alexanderjgshort/Leonhart/Multi_Protocol_Radio.kicad_sch

## KiCad design Multi_Protocol_Radio.kicad_sch (2026-04-30)

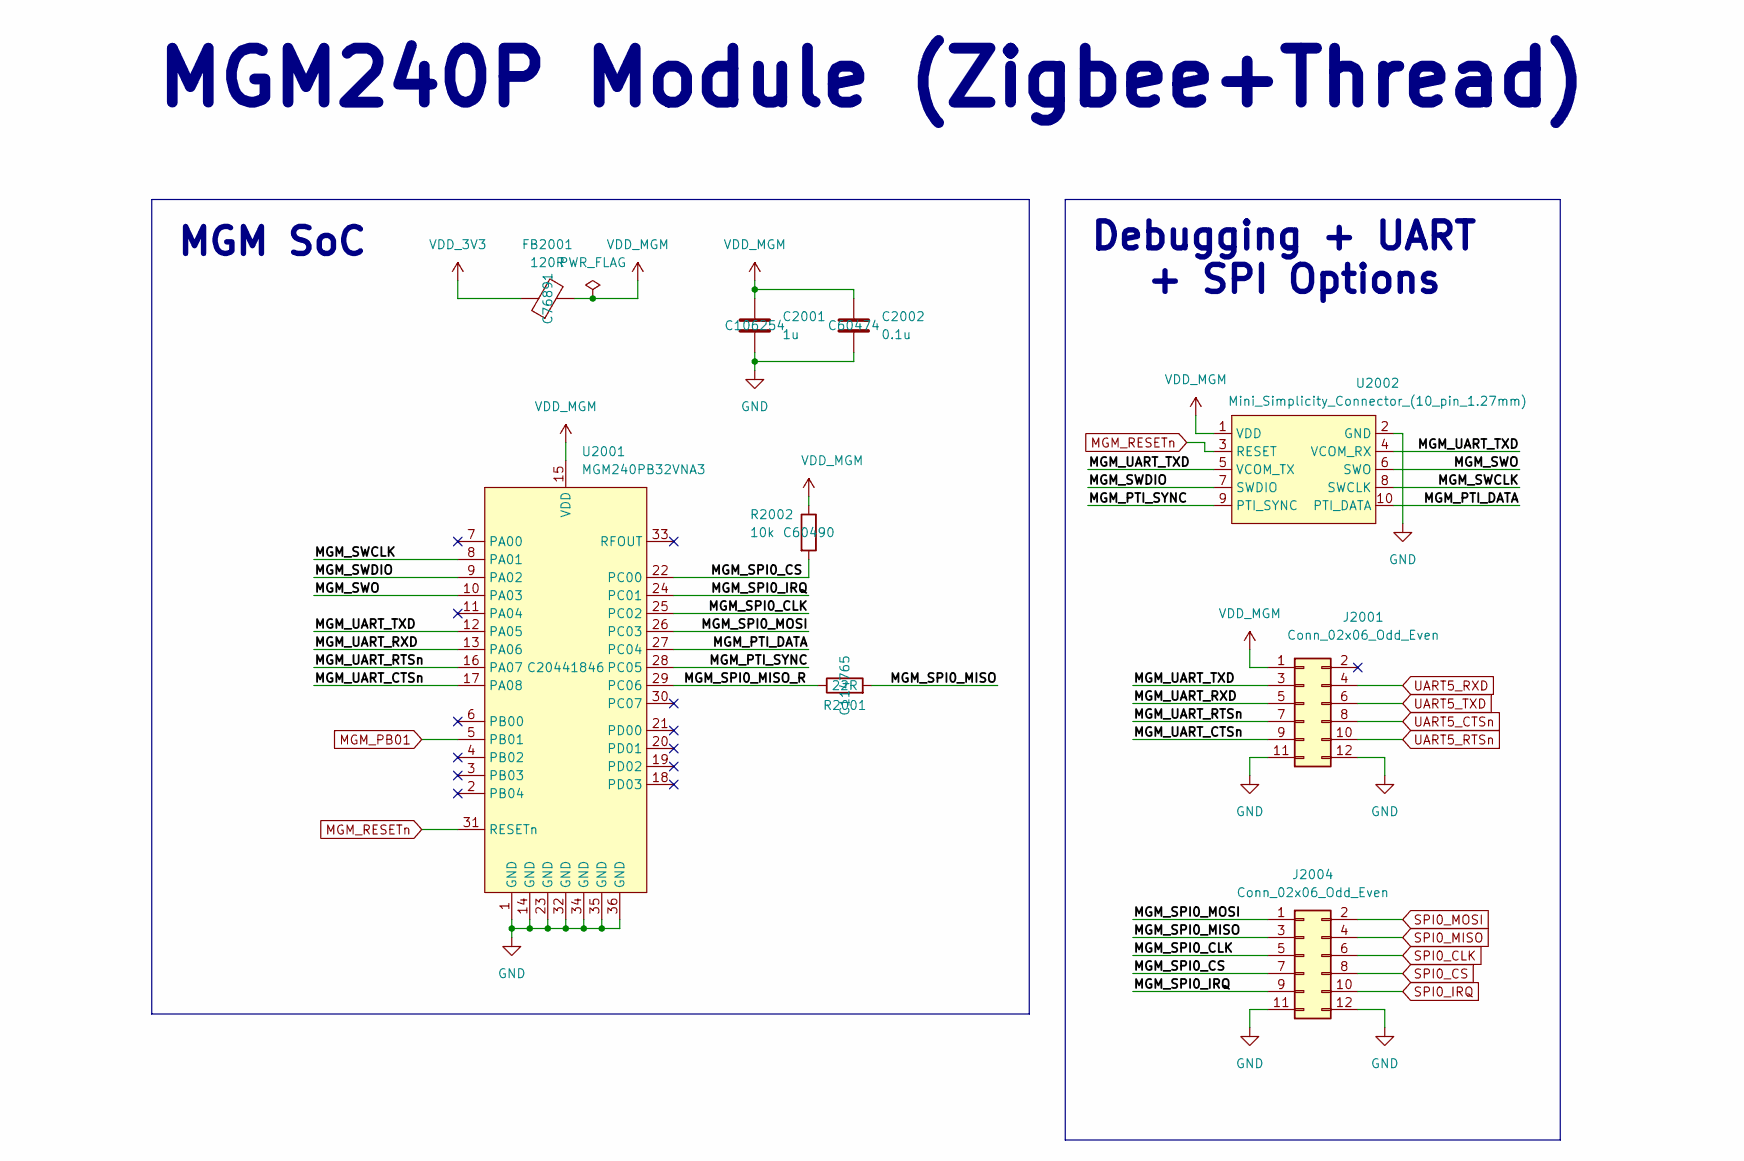
[picture p2: schematic Multi_Protocol_Radio.kicad_sch]

Parts:
C2001: 1u; C_0402_1005Metric; JLCPCB Part# C106254
C2002: 0.1u; C_0402_1005Metric; JLCPCB Part# C60474
FB2001: 120R; R_0402_1005Metric; JLCPCB Part# C76891
J2001, J2004: Conn_02x06_Odd_Even; PinHeader_2x06_P2.54mm_Vertical
R2001: 22R; R_0402_1005Metric; JLCPCB Part# C114765
R2002: 10k; R_0402_1005Metric; JLCPCB Part# C60490
U2001: MGM240PB32VNA3; JLCPCB Part# C20441846
U2002: Mini_Simplicity_Connector_(10_pin_1.27mm); FTSH10501LDVK

Connections:
GND: C2001.2, C2002.2, J2001.11, J2001.12, J2004.11, J2004.12, U2001.1 (GND), U2001.14 (GND), U2001.23 (GND), U2001.32 (GND), U2001.34 (GND), U2001.35 (GND), U2001.36 (GND), U2002.2 (GND)
MGM_PB01: U2001.5 (PB01)
MGM_PTI_DATA: U2001.27 (PC04), U2002.10 (PTI_DATA)
MGM_PTI_SYNC: U2001.28 (PC05), U2002.9 (PTI_SYNC)
MGM_RESETn: U2001.31 (RESETn), U2002.3 (RESET)
MGM_SPI0_CLK: J2004.5, U2001.25 (PC02)
MGM_SPI0_CS: J2004.7, R2002.2, U2001.22 (PC00)
MGM_SPI0_IRQ: J2004.9, U2001.24 (PC01)
MGM_SPI0_MISO: J2004.3, R2001.2
MGM_SPI0_MISO_R: R2001.1, U2001.29 (PC06)
MGM_SPI0_MOSI: J2004.1, U2001.26 (PC03)
MGM_SWCLK: U2001.8 (PA01), U2002.8 (SWCLK)
MGM_SWDIO: U2001.9 (PA02), U2002.7 (SWDIO)
MGM_SWO: U2001.10 (PA03), U2002.6 (SWO)
MGM_UART_CTSn: J2001.9, U2001.17 (PA08)
MGM_UART_RTSn: J2001.7, U2001.16 (PA07)
MGM_UART_RXD: J2001.5, U2001.13 (PA06)
MGM_UART_TXD: J2001.3, U2001.12 (PA05), U2002.4 (VCOM_RX), U2002.5 (VCOM_TX)
SPI0_CLK: J2004.6
SPI0_CS: J2004.8
SPI0_IRQ: J2004.10
SPI0_MISO: J2004.4
SPI0_MOSI: J2004.2
UART5_CTSn: J2001.8
UART5_RTSn: J2001.10
UART5_RXD: J2001.4
UART5_TXD: J2001.6
VDD_3V3: FB2001.1
VDD_MGM: C2001.1, C2002.1, FB2001.2, J2001.1, R2002.1, U2001.15 (VDD), U2002.1 (VDD)

Notes on the sheet:
Debugging + UART + SPI Options
MGM SoC
MGM240P Module (Zigbee+Thread)
