alexanderjgshort/Leonhart/hostsystem.kicad_sch

## KiCad design hostsystem.kicad_sch (2026-04-30)

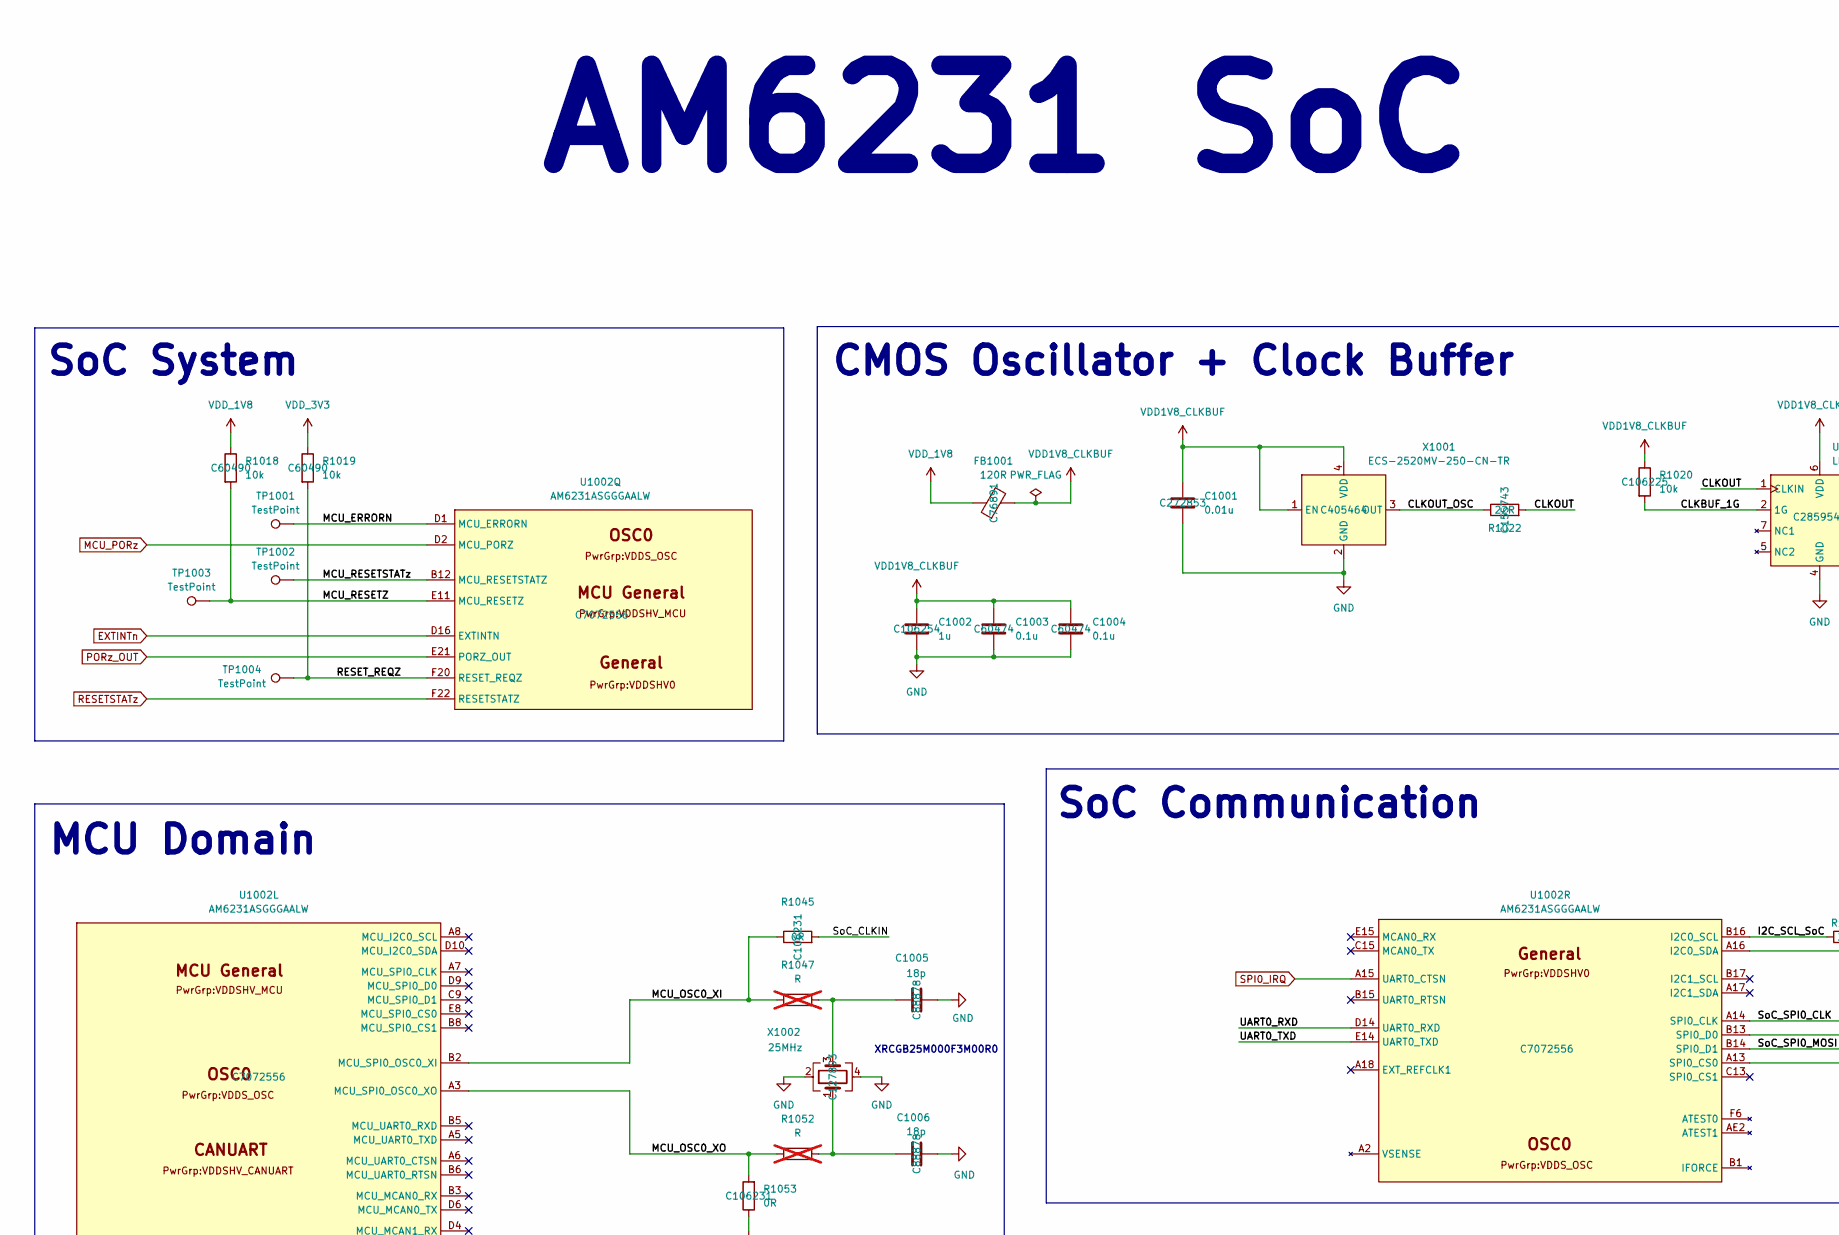
[picture p3: schematic hostsystem.kicad_sch, part in row 1, column 1]

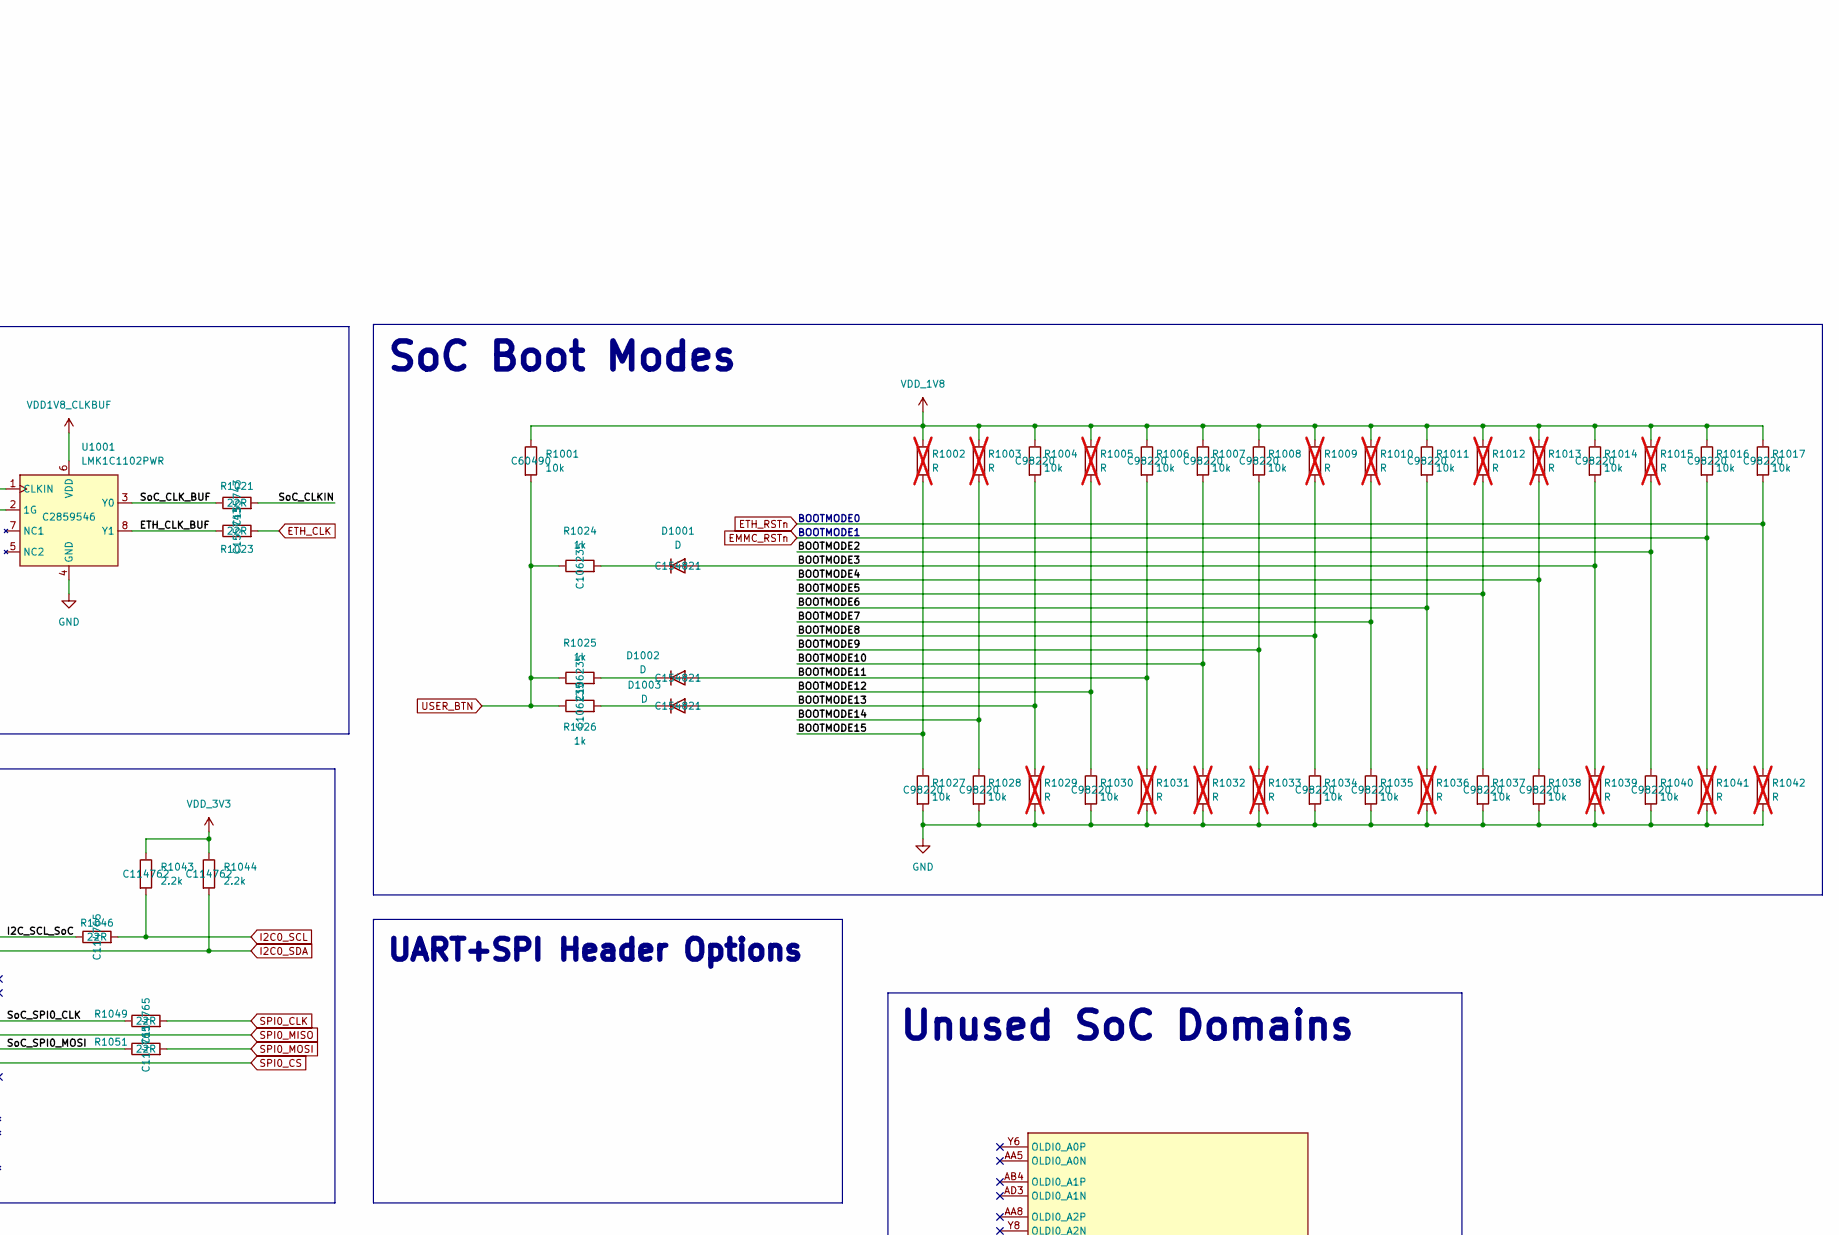
[picture p4: schematic hostsystem.kicad_sch, part in row 1, column 2]

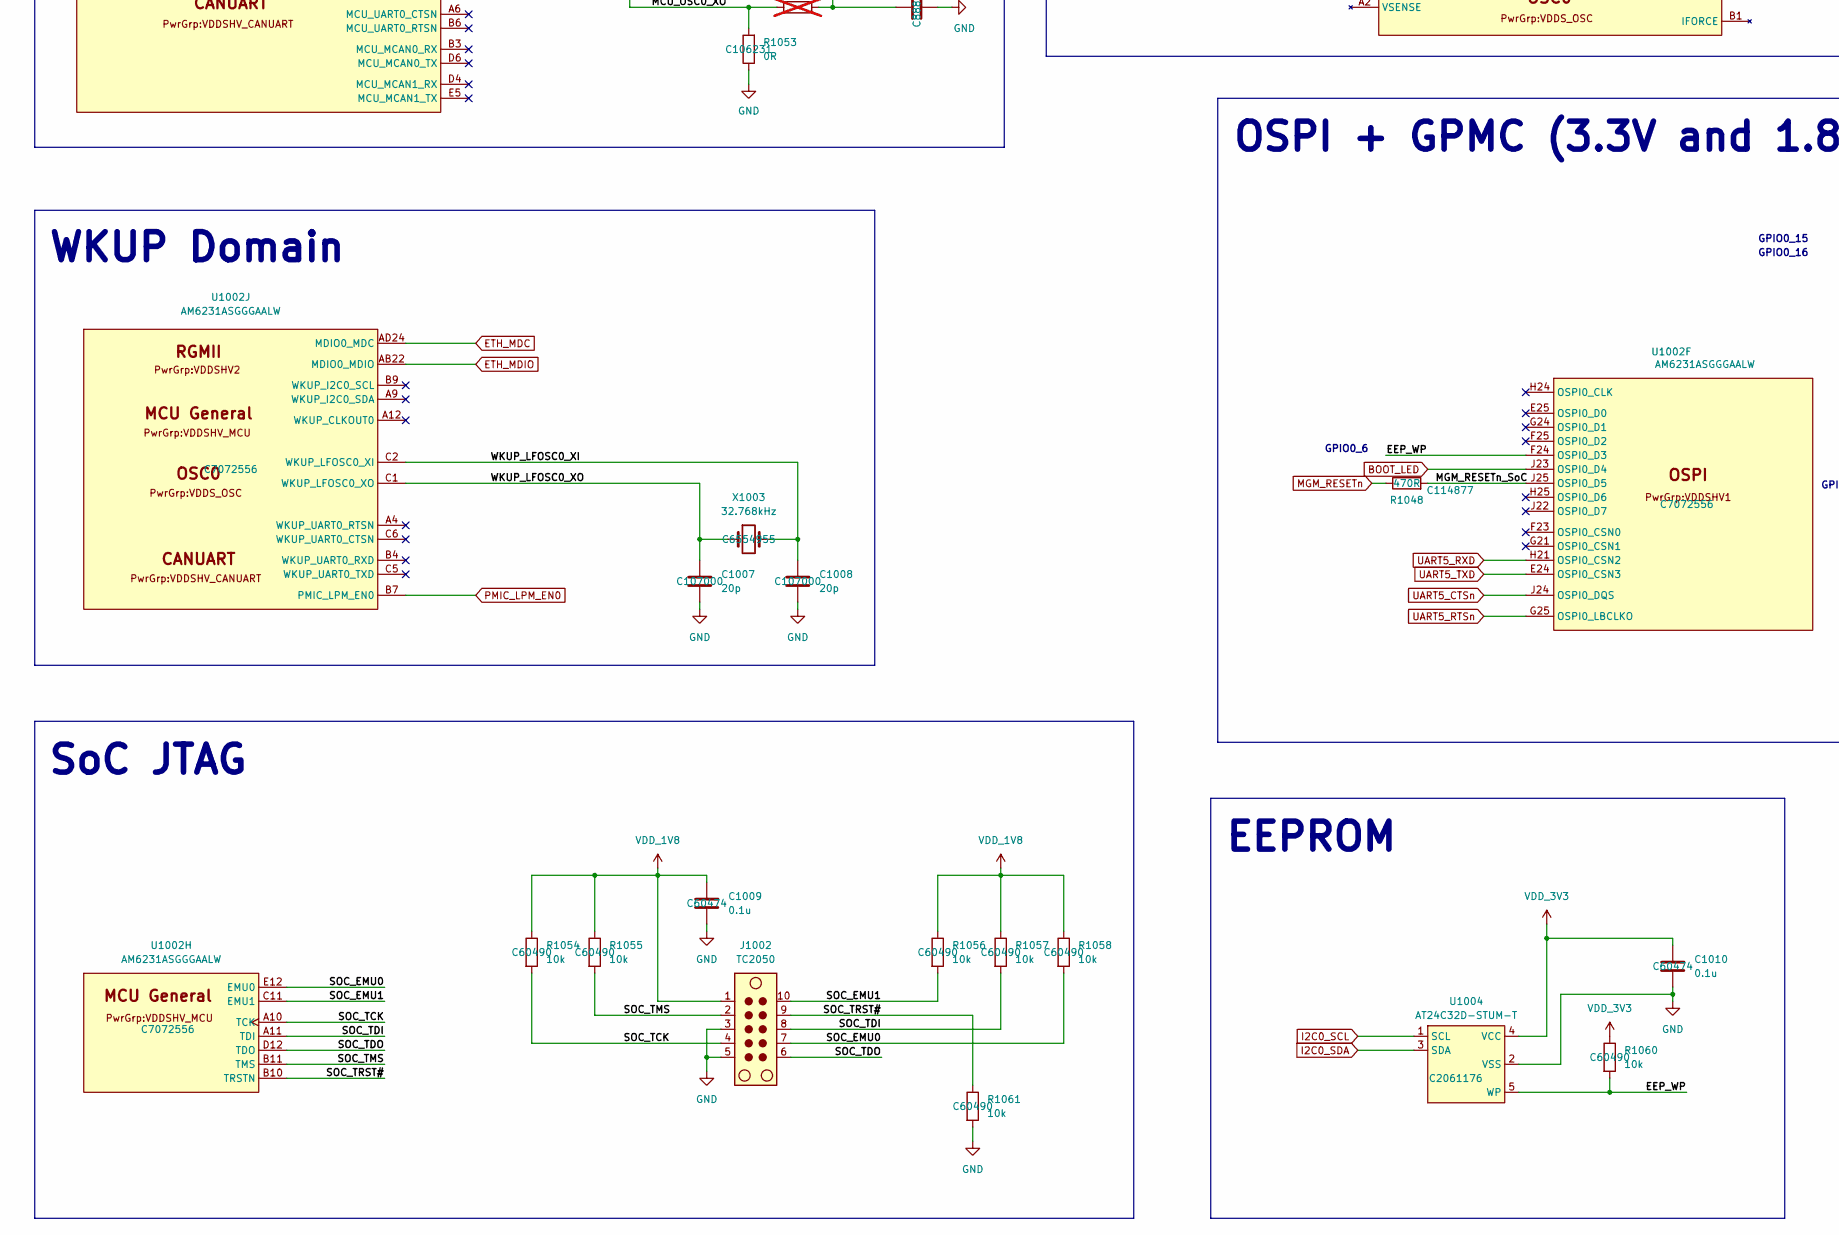
[picture p5: schematic hostsystem.kicad_sch, part in row 2, column 1]

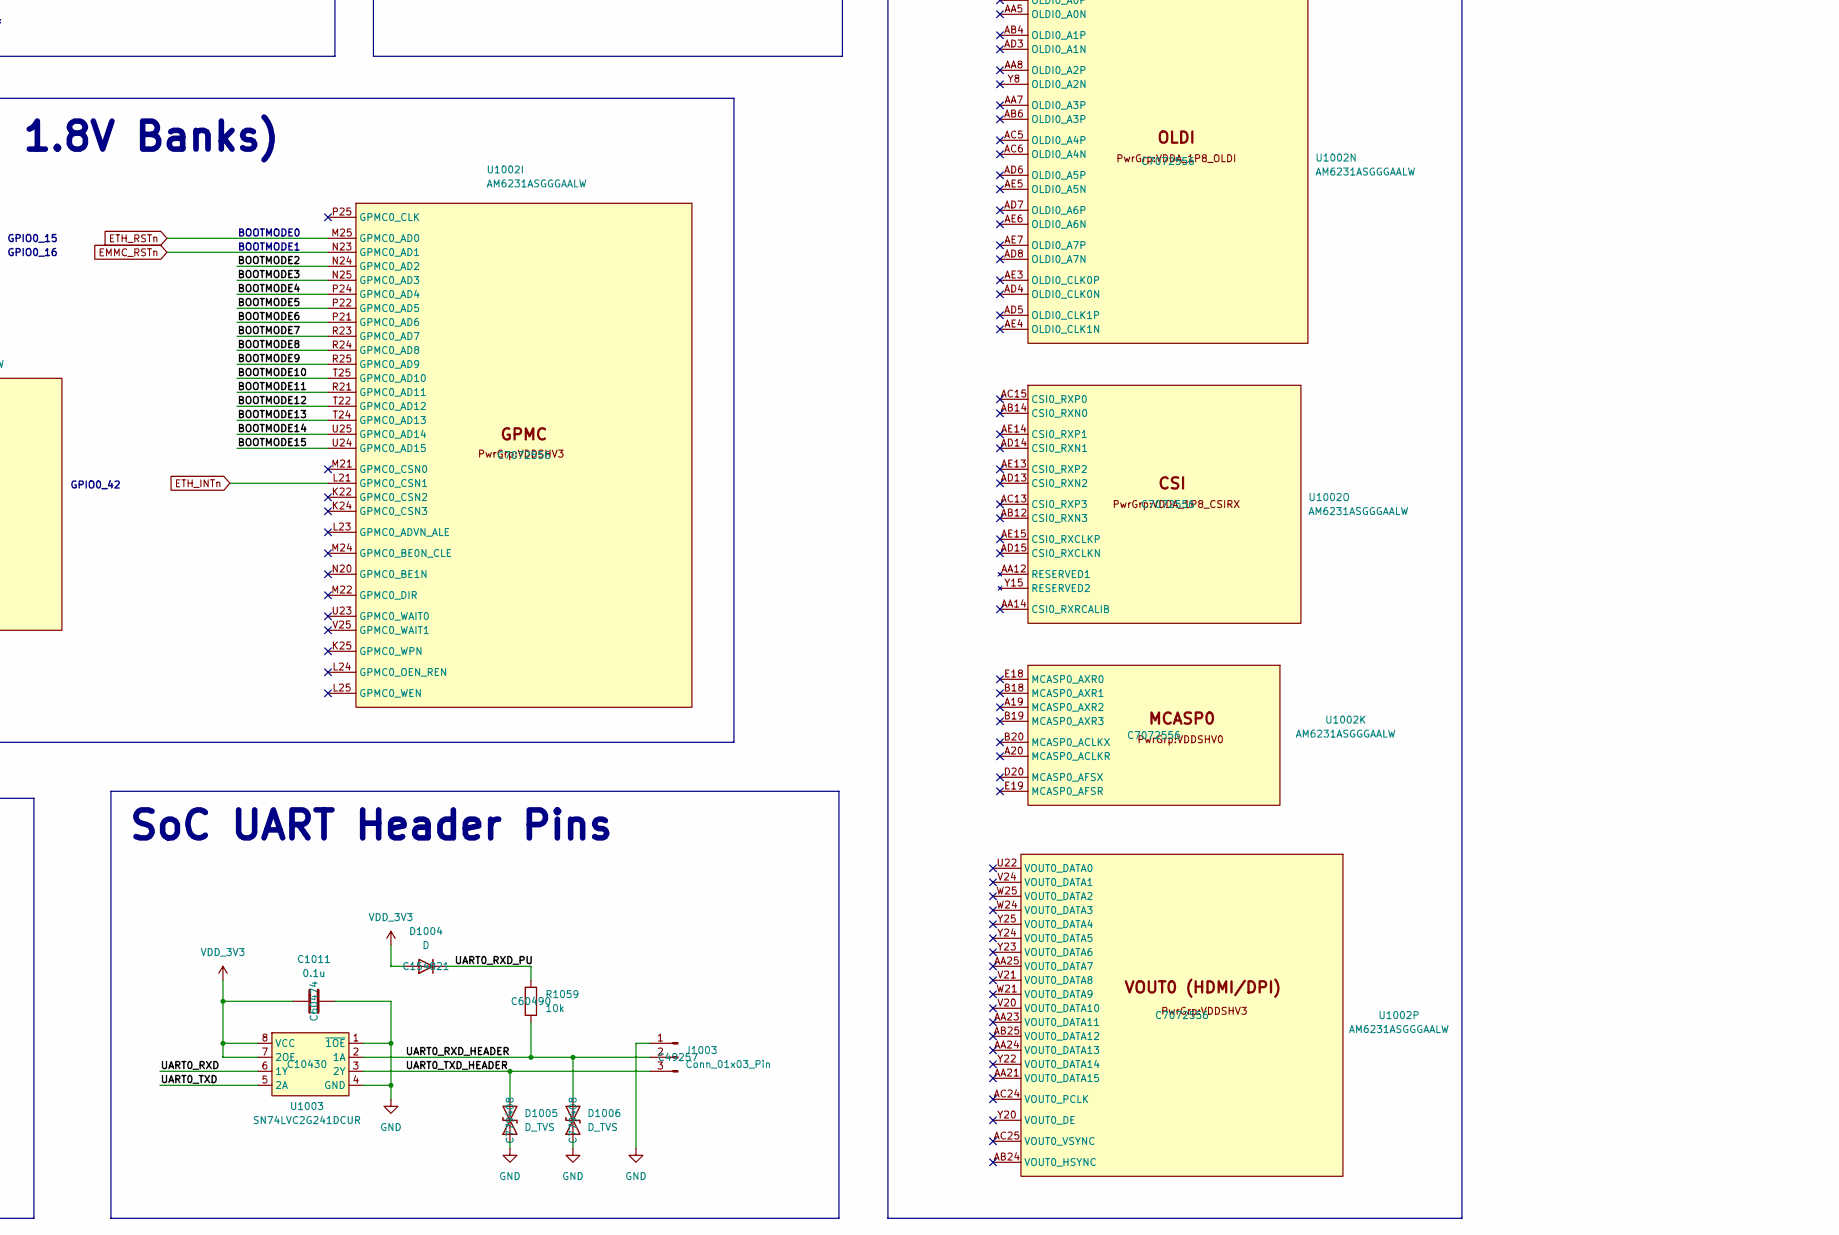
[picture p6: schematic hostsystem.kicad_sch, part in row 2, column 2]

Parts:
C1001: 0.01u; C_0201_0603Metric; JLCPCB Part# C272853
C1002: 1u; C_0402_1005Metric; JLCPCB Part# C106254
C1003, C1004, C1009, C1010, C1011: 0.1u; C_0402_1005Metric; JLCPCB Part# C60474
C1005, C1006: 18p; C_0402_1005Metric; JLCPCB Part# C88878
C1007, C1008: 20p; C_0402_1005Metric; JLCPCB Part# C107000
D1001, D1002, D1003, D1004: D; D_SOD-523; JLCPCB Part# C154821
D1005, D1006: D_TVS; TPD1E1B04DPYR; JLCPCB Part# C779408
FB1001: 120R; R_0402_1005Metric; JLCPCB Part# C76891
J1002: TC2050; Tag-Connect_TC2050-IDC-NL_2x05_P1.27mm_Vertical
J1003: Conn_01x03_Pin; PinHeader_1x03_P2.54mm_Vertical; JLCPCB Part# C49257
R1001, R1018, R1019, R1054, R1055, R1056, R1057, R1058, R1059, R1060, R1061: 10k; R_0402_1005Metric; JLCPCB Part# C60490
R1002, R1003, R1005, R1009, R1010, R1012, R1013, R1015, R1029, R1031, R1032, R1033, R1036, R1039, R1041, R1042: R; R_0603_1608Metric; not fitted
R1004, R1006, R1007, R1008, R1011, R1014, R1016, R1017, R1027, R1028, R1030, R1034, R1035, R1037, R1038, R1040: 10k; R_0603_1608Metric; JLCPCB Part# C98220
R1020: 10k; R_0201_0603Metric; JLCPCB Part# C106225
R1021, R1022, R1023: 22R; R_0201_0603Metric; JLCPCB Part# C155743
R1024, R1025, R1026: 1k; R_0402_1005Metric; JLCPCB Part# C106235
R1043, R1044: 2.2k; R_0402_1005Metric; JLCPCB Part# C114762
R1045, R1053: 0R; R_0402_1005Metric; JLCPCB Part# C106231
R1046, R1049, R1051: 22R; R_0402_1005Metric; JLCPCB Part# C114765
R1047, R1052: R; R_0402_1005Metric; not fitted
R1048: 470R; R_0402_1005Metric; JLCPCB Part# C114877
TP1001, TP1002, TP1003, TP1004: TestPoint; TestPoint_Pad_1.0x1.0mm
U1001: LMK1C1102PWR; SOP65P640X120-8N; JLCPCB Part# C2859546
U1002: AM6231ASGGGAALW; BGA425C50P25X25_1300X1300X89; JLCPCB Part# C7072556
U1003: SN74LVC2G241DCUR; SOP50P310X90-8N; JLCPCB Part# C10430
U1004: AT24C32D-STUM-T; SOT-23-5; JLCPCB Part# C2061176
X1001: ECS-2520MV-250-CN-TR; ECS2520MV250CNTR; JLCPCB Part# C405464
X1002: 25MHz; Crystal_SMD_2016-4Pin_2.0x1.6mm; JLCPCB Part# C127893
X1003: 32.768kHz; FC-135R 32.7680KA-A3; JLCPCB Part# C6554955

Connections:
BOOTMODE2: R1015.2, R1040.1, U1002.N24 (GPMC0_AD2)
BOOTMODE3: D1001.2 (A), R1014.2, R1039.1, U1002.N25 (GPMC0_AD3)
BOOTMODE4: R1013.2, R1038.1, U1002.P24 (GPMC0_AD4)
BOOTMODE5: R1012.2, R1037.1, U1002.P22 (GPMC0_AD5)
BOOTMODE6: R1011.2, R1036.1, U1002.P21 (GPMC0_AD6)
BOOTMODE7: R1010.2, R1035.1, U1002.R23 (GPMC0_AD7)
BOOTMODE8: R1009.2, R1034.1, U1002.R24 (GPMC0_AD8)
BOOTMODE9: R1008.2, R1033.1, U1002.R25 (GPMC0_AD9)
BOOTMODE10: R1007.2, R1032.1, U1002.T25 (GPMC0_AD10)
BOOTMODE11: D1002.2 (A), R1006.2, R1031.1, U1002.R21 (GPMC0_AD11)
BOOTMODE12: R1005.2, R1030.1, U1002.T22 (GPMC0_AD12)
BOOTMODE13: D1003.2 (A), R1004.2, R1029.1, U1002.T24 (GPMC0_AD13)
BOOTMODE14: R1003.2, R1028.1, U1002.U25 (GPMC0_AD14)
BOOTMODE15: R1002.2, R1027.1, U1002.U24 (GPMC0_AD15)
BOOT_LED: U1002.J23 (OSPI0_D4)
CLKBUF_1G: R1020.2, U1001.2 (1G)
CLKOUT: R1022.2, U1001.1 (CLKIN)
CLKOUT_OSC: R1022.1, X1001.3 (OUT)
EEP_WP: R1060.2, U1002.F24 (OSPI0_D3), U1004.5 (WP)
EMMC_RSTn: R1016.2, R1041.1, U1002.N23 (GPMC0_AD1)
ETH_CLK: R1023.2
ETH_CLK_BUF: R1023.1, U1001.8 (Y1)
ETH_INTn: U1002.L21 (GPMC0_CSN1)
ETH_MDC: U1002.AD24 (MDIO0_MDC)
ETH_MDIO: U1002.AB22 (MDIO0_MDIO)
ETH_RSTn: R1017.2, R1042.1, U1002.M25 (GPMC0_AD0)
EXTINTn: U1002.D16 (EXTINTN)
GND: C1001.2, C1002.2, C1003.2, C1004.2, C1005.2, C1006.2, C1007.2, C1008.2, C1009.2, C1010.2, C1011.2, D1005.1 (A1), D1006.1 (A1), J1002.3, J1002.5, J1003.1, R1027.2, R1028.2, R1029.2, R1030.2, R1031.2, R1032.2, R1033.2, R1034.2, R1035.2, R1036.2, R1037.2, R1038.2, R1039.2, R1040.2, R1041.2, R1042.2, R1053.1, R1061.2, U1001.4 (GND), U1003.1 (~1OE), U1003.4 (GND), U1004.2 (VSS), X1001.2 (GND), X1002.2, X1002.4
I2C0_SCL: R1043.2, R1046.2, U1004.1 (SCL)
I2C0_SDA: R1044.2, U1002.A16 (I2C0_SDA), U1004.3 (SDA)
I2C_SCL_SoC: R1046.1, U1002.B16 (I2C0_SCL)
MCU_ERRORN: TP1001.1, U1002.D1 (MCU_ERRORN)
MCU_OSC0_XI: R1045.1, R1047.1, U1002.B2 (MCU_SPI0_OSC0_XI)
MCU_OSC0_XO: R1052.1, R1053.2, U1002.A3 (MCU_SPI0_OSC0_XO)
MCU_PORz: U1002.D2 (MCU_PORZ)
MCU_RESETSTATz: TP1002.1, U1002.B12 (MCU_RESETSTATZ)
MCU_RESETZ: R1018.2, TP1003.1, U1002.E11 (MCU_RESETZ)
MGM_RESETn: R1048.1
MGM_RESETn_SoC: R1048.2, U1002.J25 (OSPI0_D5)
unnamed: C1005.1, R1047.2, X1002.3
unnamed: C1006.1, R1052.2, X1002.1
unnamed: D1001.1 (K), R1024.2
unnamed: D1002.1 (K), R1025.2
unnamed: D1003.1 (K), R1026.2
PMIC_LPM_EN0: U1002.B7 (PMIC_LPM_EN0)
PORz_OUT: U1002.E21 (PORZ_OUT)
RESETSTATz: U1002.F22 (RESETSTATZ)
RESET_REQZ: R1019.2, TP1004.1, U1002.F20 (RESET_REQZ)
SOC_EMU0: J1002.7, R1058.2, U1002.E12 (EMU0)
SOC_EMU1: J1002.10, R1056.2, U1002.C11 (EMU1)
SOC_TCK: J1002.4, R1054.2, U1002.A10 (TCK)
SOC_TDI: J1002.8, R1057.2, U1002.A11 (TDI)
SOC_TDO: J1002.6, U1002.D12 (TDO)
SOC_TMS: J1002.2, R1055.2, U1002.B11 (TMS)
SOC_TRST#: J1002.9, R1061.1, U1002.B10 (TRSTN)
SPI0_CLK: R1049.2
SPI0_CS: U1002.A13 (SPI0_CS0)
SPI0_IRQ: U1002.A15 (UART0_CTSN)
SPI0_MISO: U1002.B13 (SPI0_D0)
SPI0_MOSI: R1051.2
SoC_CLKIN: R1021.2, R1045.2
SoC_CLK_BUF: R1021.1, U1001.3 (Y0)
SoC_SPI0_CLK: R1049.1, U1002.A14 (SPI0_CLK)
SoC_SPI0_MOSI: R1051.1, U1002.B14 (SPI0_D1)
UART0_RXD: U1002.D14 (UART0_RXD), U1003.6 (1Y)
UART0_RXD_HEADER: D1006.2 (A2), J1003.2, R1059.2, U1003.2 (1A)
UART0_RXD_PU: D1004.1 (K), R1059.1
UART0_TXD: U1002.E14 (UART0_TXD), U1003.5 (2A)
UART0_TXD_HEADER: D1005.2 (A2), J1003.3, U1003.3 (2Y)
UART5_CTSn: U1002.J24 (OSPI0_DQS)
UART5_RTSn: U1002.G25 (OSPI0_LBCLKO)
UART5_RXD: U1002.H21 (OSPI0_CSN2)
UART5_TXD: U1002.E24 (OSPI0_CSN3)
USER_BTN: R1001.2, R1024.1, R1025.1, R1026.1
VDD1V8_CLKBUF: C1001.1, C1002.1, C1003.1, C1004.1, FB1001.2, R1020.1, U1001.6 (VDD), X1001.1 (EN), X1001.4 (VDD)
VDD_1V8: C1009.1, FB1001.1, J1002.1, R1001.1, R1002.1, R1003.1, R1004.1, R1005.1, R1006.1, R1007.1, R1008.1, R1009.1, R1010.1, R1011.1, R1012.1, R1013.1, R1014.1, R1015.1, R1016.1, R1017.1, R1018.1, R1054.1, R1055.1, R1056.1, R1057.1, R1058.1
VDD_3V3: C1010.1, C1011.1, D1004.2 (A), R1019.1, R1043.1, R1044.1, R1060.1, U1003.7 (2OE), U1003.8 (VCC), U1004.4 (VCC)
WKUP_LFOSC0_XI: C1008.1, U1002.C2 (WKUP_LFOSC0_XI), X1003.2
WKUP_LFOSC0_XO: C1007.1, U1002.C1 (WKUP_LFOSC0_XO), X1003.1

Notes on the sheet:
AM6231 SoC
BOOTMODE1
CMOS Oscillator + Clock Buffer
BOOTMODE0
MCU Domain
GPIO0_42
GPIO0_6
WKUP Domain
OSPI + GPMC (3.3V and 1.8V Banks)
SoC System
SoC Boot Modes
EEPROM
Unused SoC Domains
SoC JTAG
SoC Communication
GPIO0_15
UART+SPI Header Options
XRCGB25M000F3M00R0
GPIO0_16
SoC UART Header Pins
