alexanderjgshort/Leonhart/miscellaneous.kicad_sch

## KiCad design miscellaneous.kicad_sch (2026-04-30)

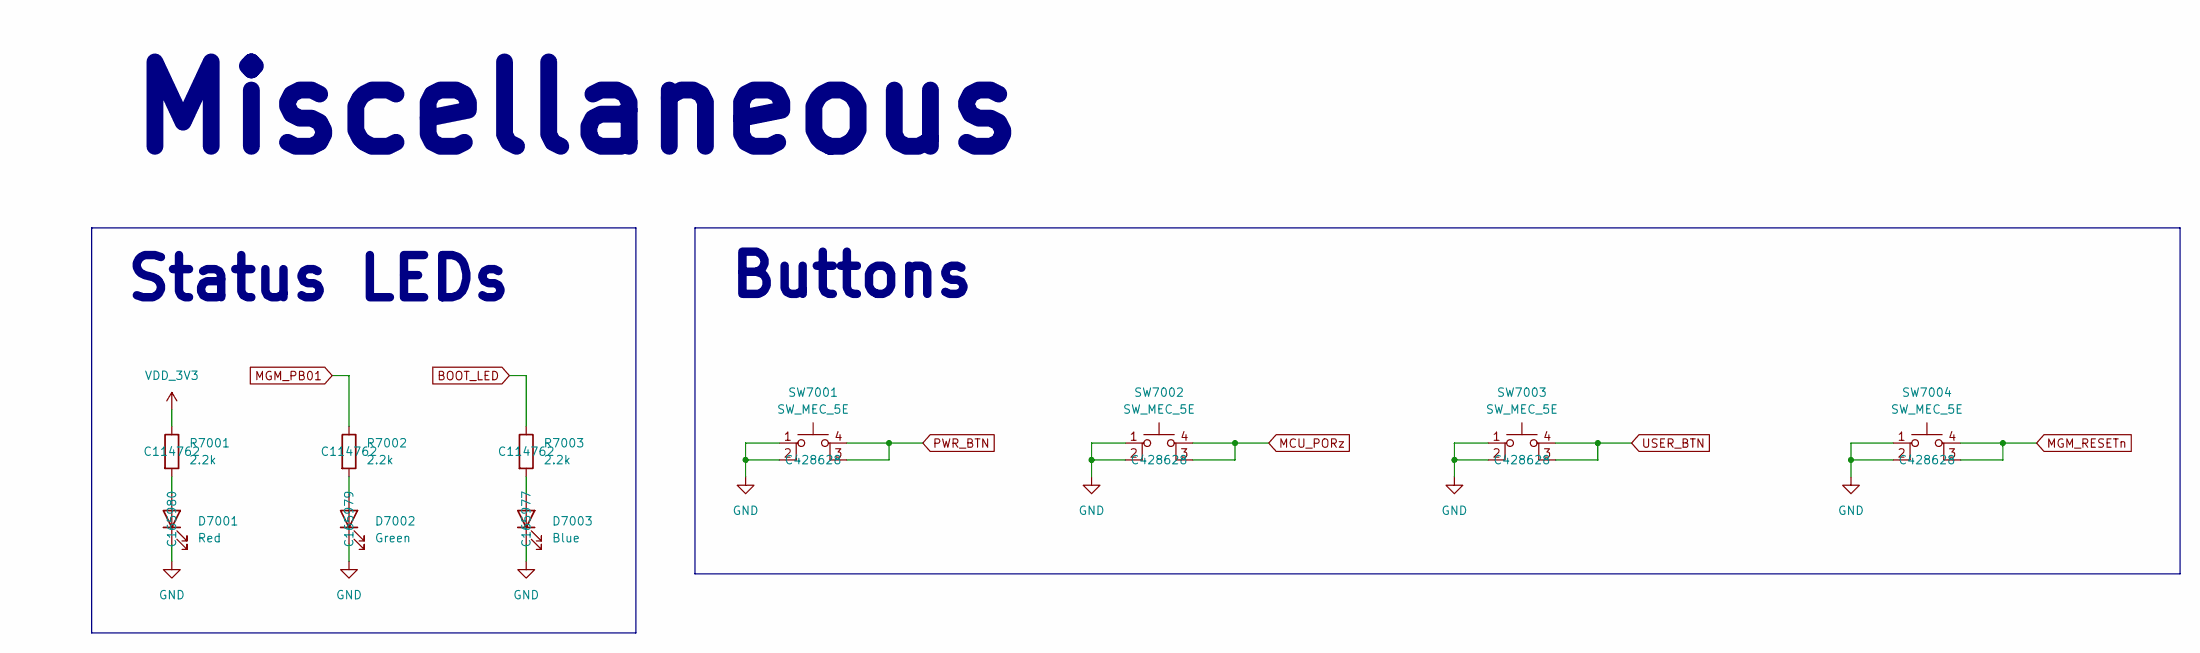
[picture p7: schematic miscellaneous.kicad_sch]

Parts:
D7001: Red; LED_0402_1005Metric; JLCPCB Part# C165980
D7002: Green; LED_0402_1005Metric; JLCPCB Part# C165979
D7003: Blue; LED_0402_1005Metric; JLCPCB Part# C165977
R7001, R7002, R7003: 2.2k; R_0402_1005Metric; JLCPCB Part# C114762
SW7001, SW7002, SW7003, SW7004: SW_MEC_5E; 1825910-6; JLCPCB Part# C428628

Connections:
BOOT_LED: R7003.1
GND: D7001.1 (K), D7002.1 (K), D7003.1 (K), SW7001.1, SW7001.2, SW7002.1, SW7002.2, SW7003.1, SW7003.2, SW7004.1, SW7004.2
MCU_PORz: SW7002.3 (K), SW7002.4 (A)
MGM_PB01: R7002.1
MGM_RESETn: SW7004.3 (K), SW7004.4 (A)
unnamed: D7001.2 (A), R7001.2
unnamed: D7002.2 (A), R7002.2
unnamed: D7003.2 (A), R7003.2
PWR_BTN: SW7001.3 (K), SW7001.4 (A)
USER_BTN: SW7003.3 (K), SW7003.4 (A)
VDD_3V3: R7001.1

Notes on the sheet:
Buttons
Miscellaneous
Status LEDs
