alexanderjgshort/Leonhart/usb_and_sd.kicad_sch

## KiCad design usb_and_sd.kicad_sch (2026-04-30)

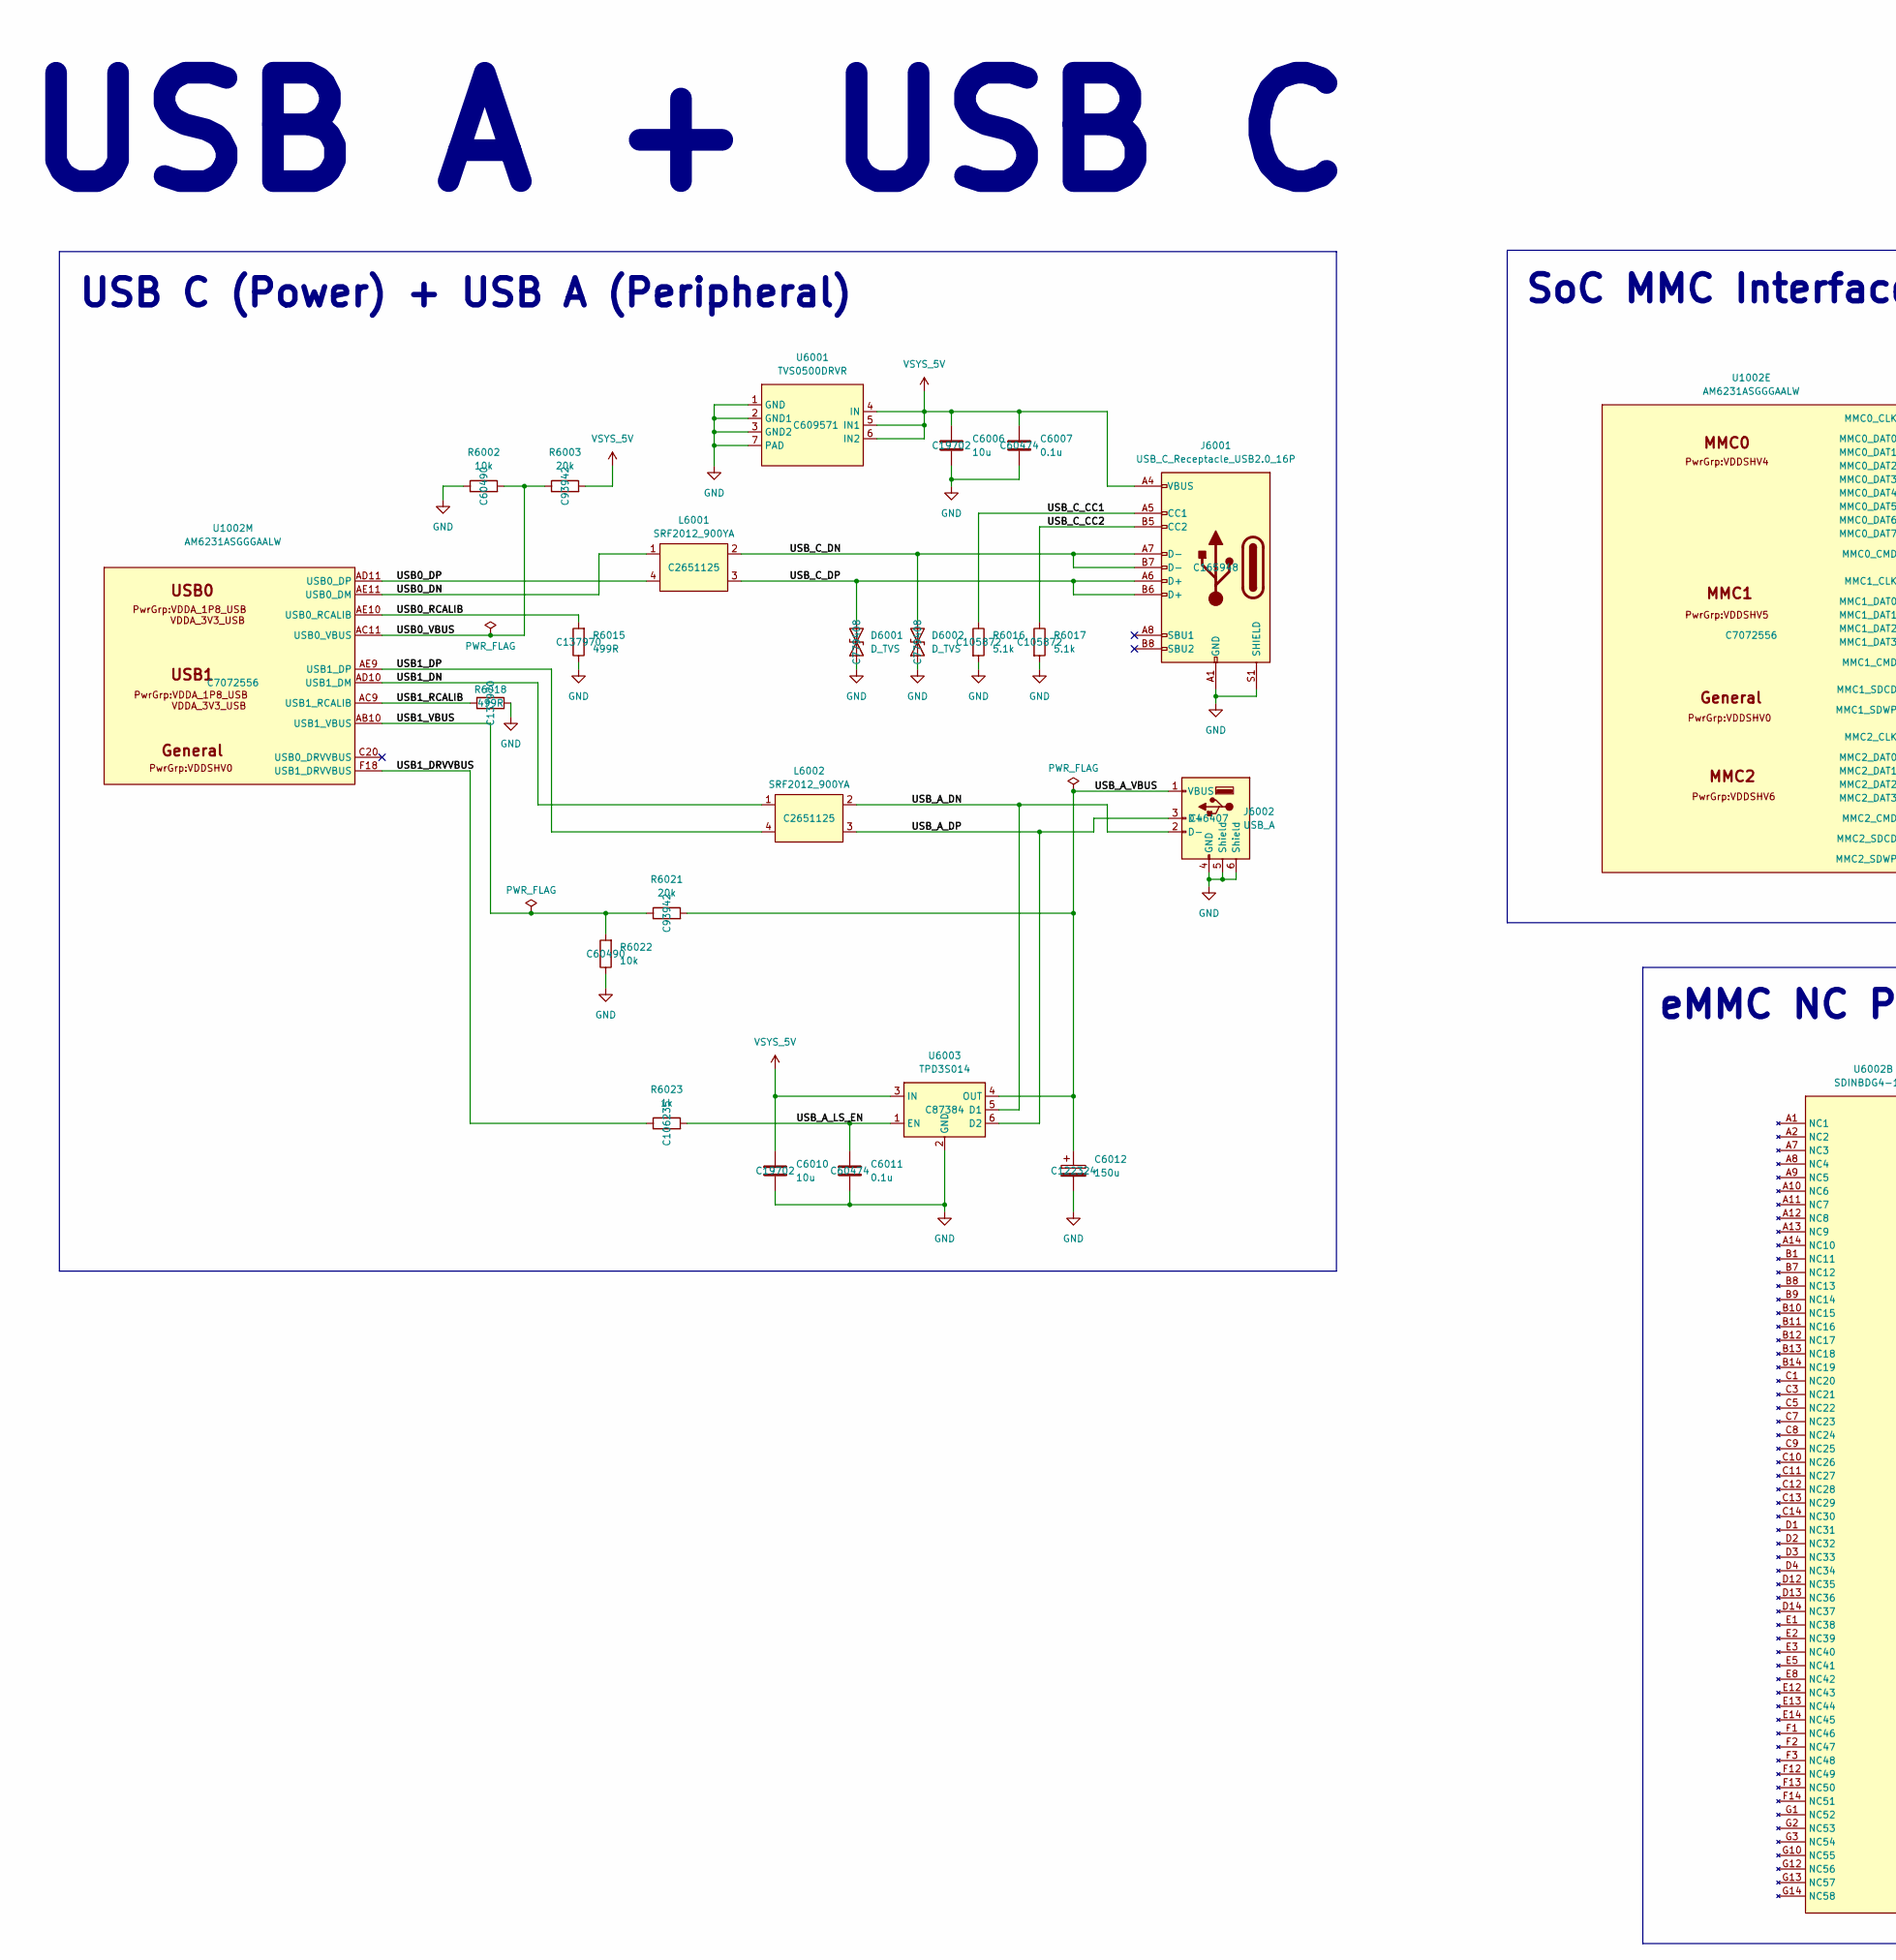
[picture p8: schematic usb_and_sd.kicad_sch, part in row 1, column 1]

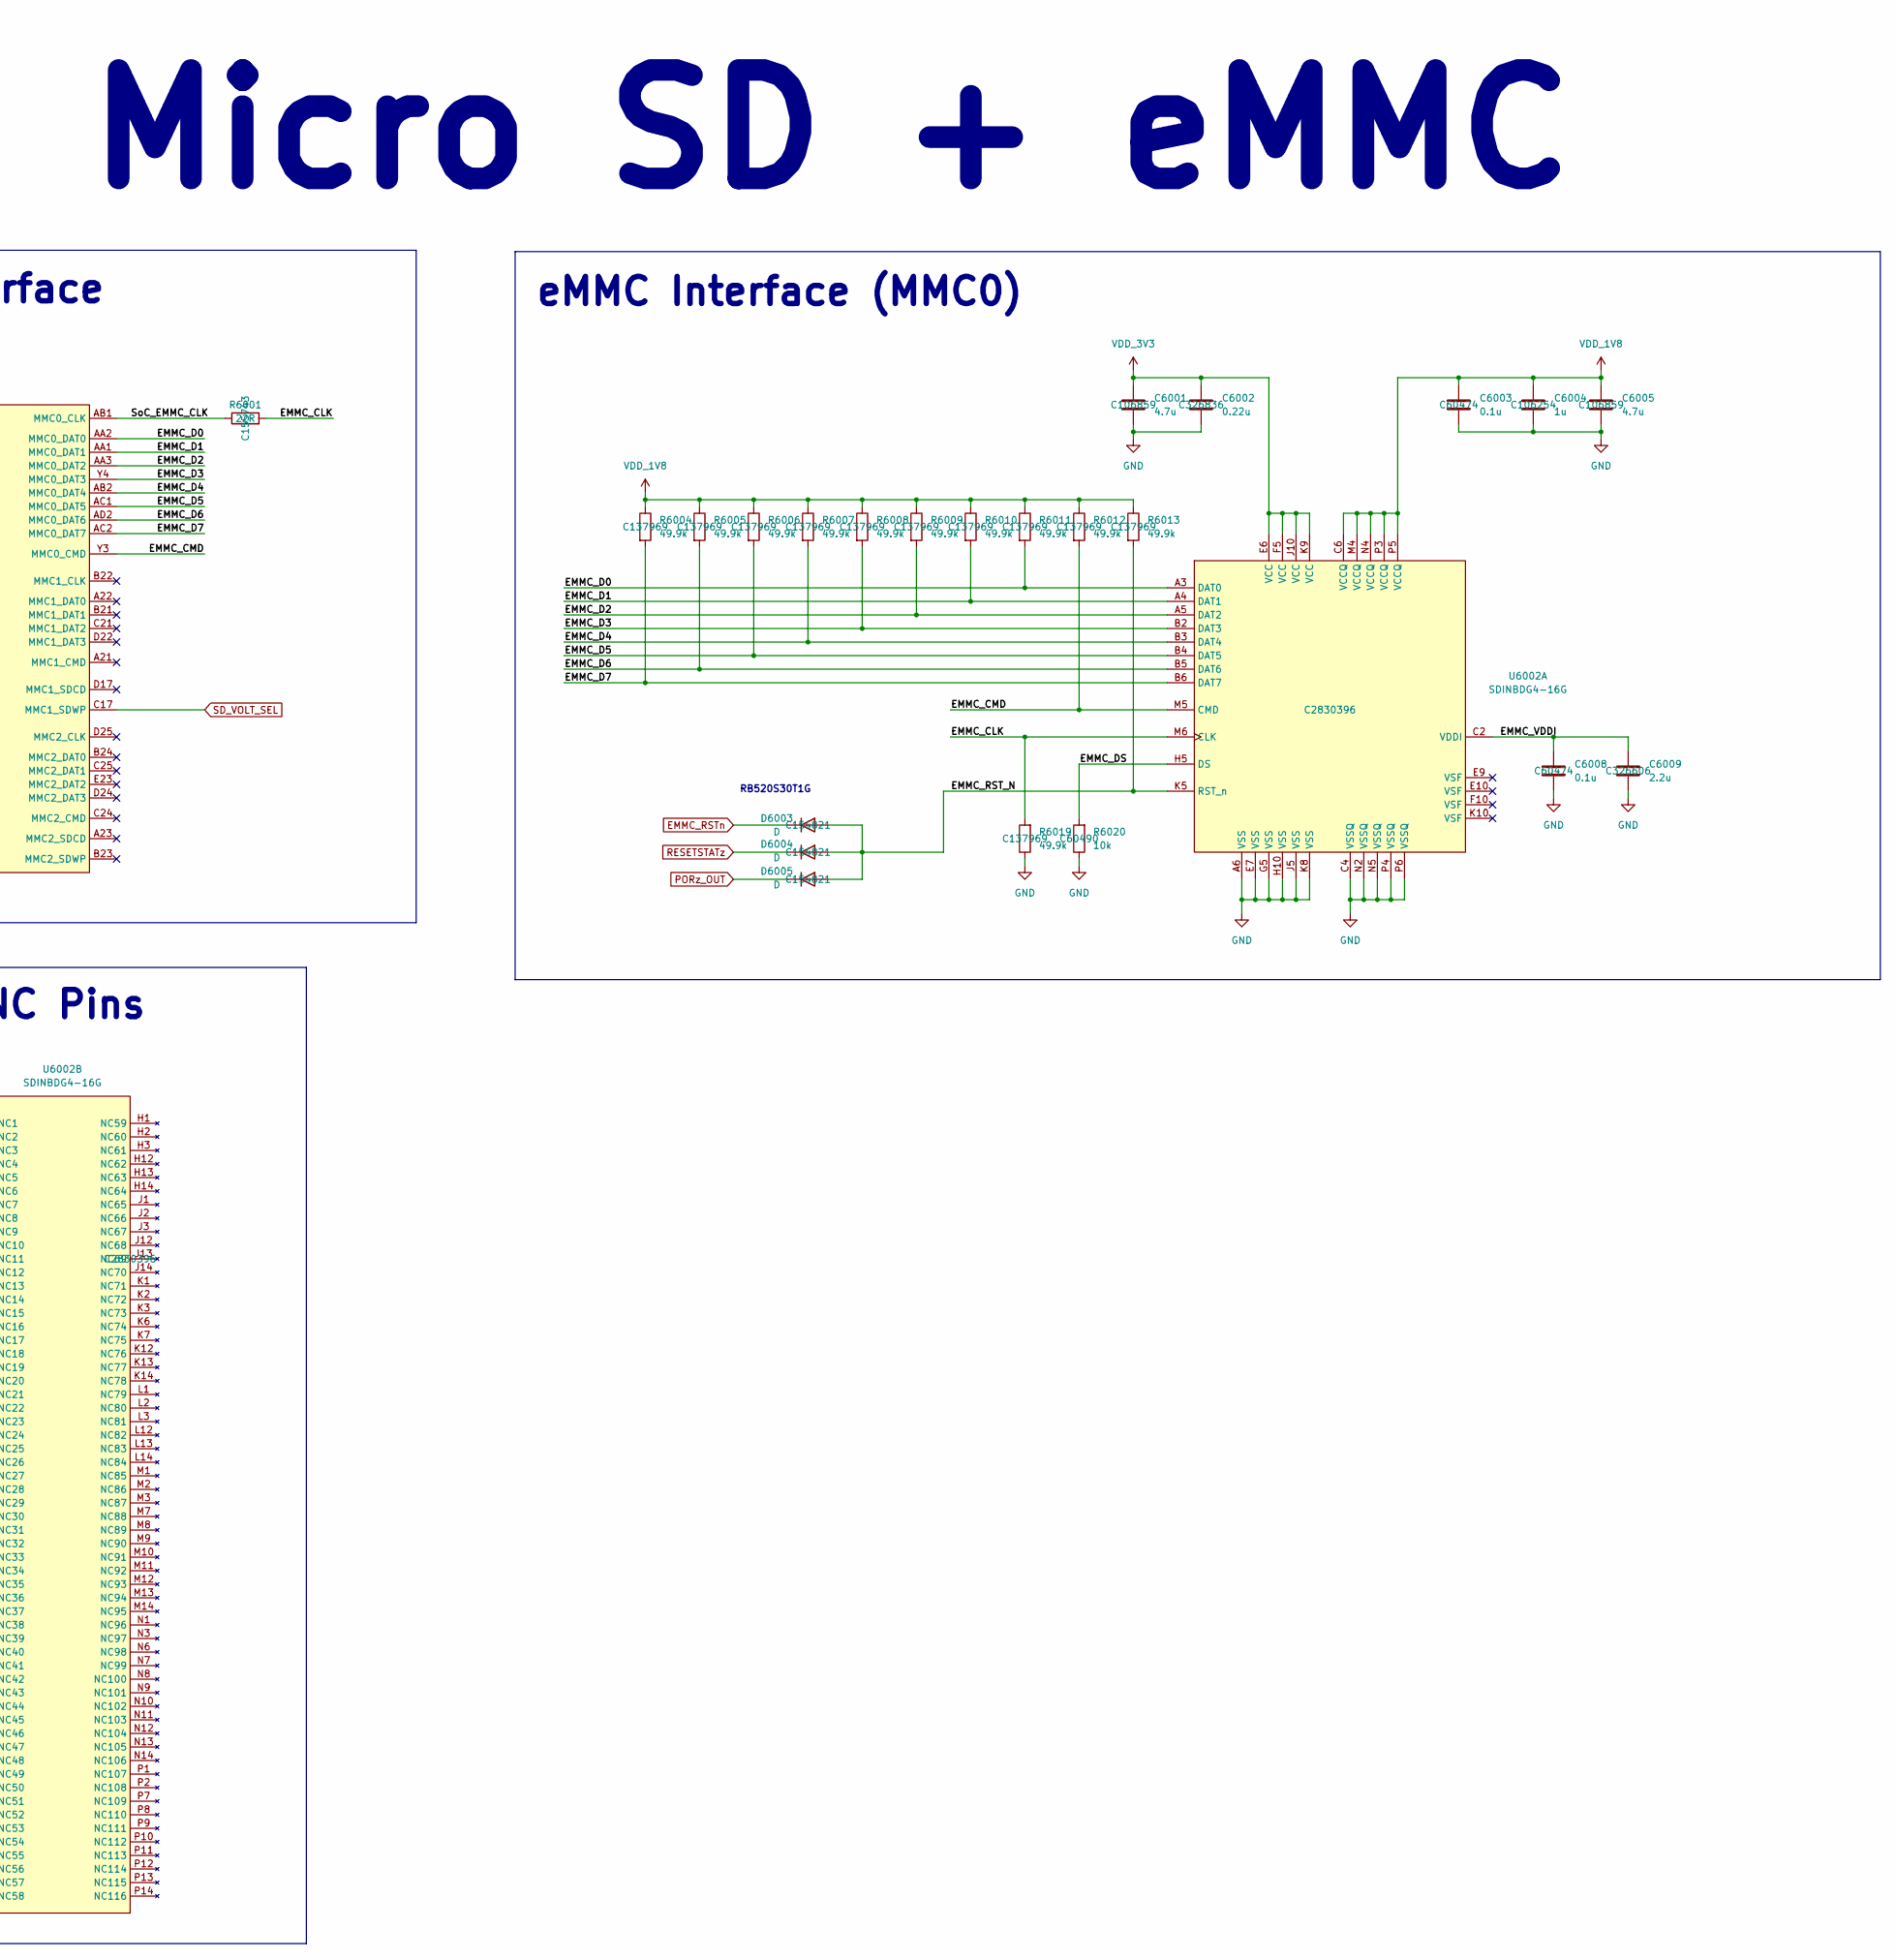
[picture p9: schematic usb_and_sd.kicad_sch, part in row 1, column 2]

Parts:
C6001, C6005: 4.7u; C_0402_1005Metric; JLCPCB Part# C106859
C6002: 0.22u; C_0402_1005Metric; JLCPCB Part# C326836
C6003, C6007, C6008, C6011: 0.1u; C_0402_1005Metric; JLCPCB Part# C60474
C6004: 1u; C_0402_1005Metric; JLCPCB Part# C106254
C6006, C6010: 10u; C_0603_1608Metric; JLCPCB Part# C19702
C6009: 2.2u; C_0402_1005Metric; JLCPCB Part# C326606
C6012: 150u; CP_EIA-7343-31_Kemet-D; JLCPCB Part# C122324
D6001, D6002: D_TVS; TPD1E1B04DPYR; JLCPCB Part# C779408
D6003, D6004, D6005: D; D_SOD-523; JLCPCB Part# C154821
J6001: USB_C_Receptacle_USB2.0_16P; USB_C_Receptacle_HRO_TYPE-C-31-M-12; JLCPCB Part# C165948
J6002: USB_A; 902131A1011D10100; JLCPCB Part# C46407
L6001, L6002: SRF2012_900YA; SRF2012-900YA; JLCPCB Part# C2651125
R6001: 22R; R_0201_0603Metric; JLCPCB Part# C155743
R6002, R6020, R6022: 10k; R_0402_1005Metric; JLCPCB Part# C60490
R6003, R6021: 20k; R_0402_1005Metric; JLCPCB Part# C93942
R6004, R6005, R6006, R6007, R6008, R6009, R6010, R6011, R6012, R6013, R6019: 49.9k; R_0402_1005Metric; JLCPCB Part# C137969
R6015, R6018: 499R; R_0402_1005Metric; JLCPCB Part# C137970
R6016, R6017: 5.1k; R_0402_1005Metric; JLCPCB Part# C105872
R6023: 1k; R_0402_1005Metric; JLCPCB Part# C106235
U1002: AM6231ASGGGAALW; BGA425C50P25X25_1300X1300X89; JLCPCB Part# C7072556
U6001: TVS0500DRVR; WSON-6-1EP_2x2mm_P0.65mm_EP1x1.6mm; JLCPCB Part# C609571
U6002: SDINBDG4-16G; LFBGA-153_11.5x13mm_Layout14x14_P0.5mm; JLCPCB Part# C2830396
U6003: TPD3S014; SOT-23-6; JLCPCB Part# C87384

Connections:
EMMC_CLK: R6001.2, R6019.2, U6002.M6 (CLK)
EMMC_CMD: R6012.2, U1002.Y3 (MMC0_CMD), U6002.M5 (CMD)
EMMC_D0: R6011.2, U1002.AA2 (MMC0_DAT0), U6002.A3 (DAT0)
EMMC_D1: R6010.2, U1002.AA1 (MMC0_DAT1), U6002.A4 (DAT1)
EMMC_D2: R6009.2, U1002.AA3 (MMC0_DAT2), U6002.A5 (DAT2)
EMMC_D3: R6008.2, U1002.Y4 (MMC0_DAT3), U6002.B2 (DAT3)
EMMC_D4: R6007.2, U1002.AB2 (MMC0_DAT4), U6002.B3 (DAT4)
EMMC_D5: R6006.2, U1002.AC1 (MMC0_DAT5), U6002.B4 (DAT5)
EMMC_D6: R6005.2, U1002.AD2 (MMC0_DAT6), U6002.B5 (DAT6)
EMMC_D7: R6004.2, U1002.AC2 (MMC0_DAT7), U6002.B6 (DAT7)
EMMC_DS: R6020.2, U6002.H5 (DS)
EMMC_RST_N: D6003.2 (A), D6004.2 (A), D6005.2 (A), R6013.2, U6002.K5 (RST_n)
EMMC_RSTn: D6003.1 (K)
EMMC_VDDI: C6008.1, C6009.1, U6002.C2 (VDDI)
GND: C6001.2, C6002.2, C6003.2, C6004.2, C6005.2, C6006.2, C6007.2, C6008.2, C6009.2, C6010.2, C6011.2, C6012.2, D6001.1 (A1), D6002.1 (A1), J6001.A1 (GND), J6001.A12 (GND), J6001.B1 (GND), J6001.B12 (GND), J6001.S1 (SHIELD), J6002.4 (GND), J6002.5 (Shield), J6002.6 (Shield), R6002.1, R6015.1, R6016.2, R6017.2, R6018.1, R6019.1, R6020.1, R6022.1, U6001.1 (GND), U6001.2 (GND1), U6001.3 (GND2), U6001.7 (PAD), U6002.A6 (VSS), U6002.C4 (VSSQ), U6002.E7 (VSS), U6002.G5 (VSS), U6002.H10 (VSS), U6002.J5 (VSS), U6002.K8 (VSS), U6002.N2 (VSSQ), U6002.N5 (VSSQ), U6002.P4 (VSSQ), U6002.P6 (VSSQ), U6003.2 (GND)
PORz_OUT: D6005.1 (K)
RESETSTATz: D6004.1 (K)
SD_VOLT_SEL: U1002.C17 (MMC1_SDWP)
SoC_EMMC_CLK: R6001.1, U1002.AB1 (MMC0_CLK)
USB0_DN: L6001.1, U1002.AE11 (USB0_DM)
USB0_DP: L6001.4, U1002.AD11 (USB0_DP)
USB0_RCALIB: R6015.2, U1002.AE10 (USB0_RCALIB)
USB0_VBUS: R6002.2, R6003.1, U1002.AC11 (USB0_VBUS)
USB1_DN: L6002.1, U1002.AD10 (USB1_DM)
USB1_DP: L6002.4, U1002.AE9 (USB1_DP)
USB1_DRVVBUS: R6023.1, U1002.F18 (USB1_DRVVBUS)
USB1_RCALIB: R6018.2, U1002.AC9 (USB1_RCALIB)
USB1_VBUS: R6021.1, R6022.2, U1002.AB10 (USB1_VBUS)
USB_A_DN: J6002.2 (D-), L6002.2, U6003.5 (D1)
USB_A_DP: J6002.3 (D+), L6002.3, U6003.6 (D2)
USB_A_LS_EN: C6011.1, R6023.2, U6003.1 (EN)
USB_A_VBUS: C6012.1, J6002.1 (VBUS), R6021.2, U6003.4 (OUT)
USB_C_CC1: J6001.A5 (CC1), R6016.1
USB_C_CC2: J6001.B5 (CC2), R6017.1
USB_C_DN: D6002.2 (A2), J6001.A7 (D-), J6001.B7 (D-), L6001.2
USB_C_DP: D6001.2 (A2), J6001.A6 (D+), J6001.B6 (D+), L6001.3
VDD_1V8: C6003.1, C6004.1, C6005.1, R6004.1, R6005.1, R6006.1, R6007.1, R6008.1, R6009.1, R6010.1, R6011.1, R6012.1, R6013.1, U6002.C6 (VCCQ), U6002.M4 (VCCQ), U6002.N4 (VCCQ), U6002.P3 (VCCQ), U6002.P5 (VCCQ)
VDD_3V3: C6001.1, C6002.1, U6002.E6 (VCC), U6002.F5 (VCC), U6002.J10 (VCC), U6002.K9 (VCC)
VSYS_5V: C6006.1, C6007.1, C6010.1, J6001.A4 (VBUS), J6001.A9 (VBUS), J6001.B4 (VBUS), J6001.B9 (VBUS), R6003.2, U6001.4 (IN), U6001.5 (IN1), U6001.6 (IN2), U6003.3 (IN)

Notes on the sheet:
USB C (Power) + USB A (Peripheral)
eMMC Interface (MMC0)
Micro SD + eMMC
RB520S30T1G
SoC MMC Interface
eMMC NC Pins
USB A + USB C
